2023-24-tfgii-online-feb/Proyecto_TFG_UBU_23_24/TFG/anexos.tex

\documentclass[a4paper,12pt,twoside]{memoir}

% Castellano
\usepackage[spanish,es-tabla]{babel}
\selectlanguage{spanish}
\usepackage[utf8]{inputenc}
\usepackage[T1]{fontenc}
\usepackage{lmodern} % scalable font
\usepackage{microtype}
\usepackage{placeins}
\usepackage{csquotes}
\usepackage{lscape} 
\usepackage[table,xcdraw]{xcolor}
\usepackage{graphicx}
\usepackage{float} %required for the placement specifier H

\usepackage{makecell}

\renewcommand\theadalign{bc}
\renewcommand\theadfont{\bfseries}
\renewcommand\theadgape{\Gape[4pt]}
\renewcommand\cellgape{\Gape[4pt]}

% Landscape
\usepackage{pdflscape}

% Mathematic font
\usepackage{amsfonts}

\RequirePackage{booktabs}
\RequirePackage[table]{xcolor}
\RequirePackage{xtab}
\RequirePackage{multirow}

% Multi-page tables using
\nouppercaseheads
\usepackage{longtable}
\usepackage{tabularx}

% Cell with line break (e.g. \specialcell{Foo\\bar})
\newcommand{\specialcell}[2][c]{%
  \begin{tabular}[#1]{@{}l@{}}#2\end{tabular}}
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
      \toprule
      #5
      \otoprule
    }
    \tabletail{
      \hline
      \multicolumn{#3}{r}{\small\sl continúa en la página siguiente}\\
    }
    \tablelasttail{
      \hline
    }
    \bottomcaption{#1}
    \rowcolors {2}{gray!35}{}
    \begin{xtabular}{#2}
      #6
      \bottomrule
    \end{xtabular}
    \label{tabla:#4}
  \end{center}
}

%
% Nuevo comando para tablas grandes con cabecera.
\newcommand{\tablaSinColores}[6]{%
  \begin{center}
    \tablefirsthead{
      \toprule
      #5
      \otoprule
    }
    \tablehead{
      \multicolumn{#3}{l}{\small\sl continúa desde la página anterior}\\
      \toprule
      #5
      \otoprule
    }
    \tabletail{
      \hline
      \multicolumn{#3}{r}{\small\sl continúa en la página siguiente}\\
    }
    \tablelasttail{
      \hline
    }
    \bottomcaption{#1}
    \begin{xtabular}{#2}
      #6
      \bottomrule
    \end{xtabular}
    \label{tabla:#4}
  \end{center}
}

%
% Nuevo comando para tablas grandes sin cabecera.
\newcommand{\tablaSinCabecera}[5]{%
  \begin{center}
    \tablefirsthead{
      \toprule
    }
    \tablehead{
      \multicolumn{#3}{l}{\small\sl continúa desde la página anterior}\\
      \hline
    }
    \tabletail{
      \hline
      \multicolumn{#3}{r}{\small\sl continúa en la página siguiente}\\
    }
    \tablelasttail{
      \hline
    }
    \bottomcaption{#1}
  \begin{xtabular}{#2}
    #5
   \bottomrule
  \end{xtabular}
  \label{tabla:#4}
  \end{center}
}

\definecolor{cgoLight}{HTML}{EEEEEE}
\definecolor{cgoExtralight}{HTML}{FFFFFF}

%
% Nuevo comando para tablas grandes sin cabecera.
\newcommand{\tablaSinCabeceraConBandas}[5]{%
  \begin{center}
    \tablefirsthead{
      \toprule
    }
    \tablehead{
      \multicolumn{#3}{l}{\small\sl continúa desde la página anterior}\\
      \hline
    }
    \tabletail{
      \hline
      \multicolumn{#3}{r}{\small\sl continúa en la página siguiente}\\
    }
    \tablelasttail{
      \hline
    }
    \bottomcaption{#1}
    \rowcolors[]{1}{cgoExtralight}{cgoLight}

  \begin{xtabular}{#2}
    #5
   \bottomrule
  \end{xtabular}
  \label{tabla:#4}
  \end{center}
}

\graphicspath{ {./img/} }

% Capítulos
\chapterstyle{bianchi}
\newcommand{\capitulo}[2]{
	\setcounter{chapter}{#1}
	\setcounter{section}{0}
	\setcounter{figure}{0}
	\setcounter{table}{0}
	\chapter*{#2}
	\addcontentsline{toc}{chapter}{#2}
	\markboth{#2}{#2}
}

% Apéndices
\renewcommand{\appendixname}{Apéndice}
\renewcommand*\cftappendixname{\appendixname}

\newcommand{\apendice}[1]{
	%\renewcommand{\thechapter}{A}
	\chapter{#1}
}

\renewcommand*\cftappendixname{\appendixname\ }

% Formato de portada
\makeatletter
\usepackage{xcolor}
\newcommand{\tutor}[1]{\def\@tutor{#1}}
\newcommand{\tutors}[1]{\def\@tutors{#1}}
\newcommand{\course}[1]{\def\@course{#1}}
\definecolor{cpardoBox}{HTML}{E6E6FF}
\def\maketitle{
  \null
  \thispagestyle{empty}
  % Cabecera ----------------
\noindent\vspace{1cm}%
  \vfill
  % Título proyecto y escudo informática ----------------
  \colorbox{cpardoBox}{%
    \begin{minipage}{.8\textwidth}
      \vspace{.5cm}\Large
      \begin{center}
      \textbf{TFG del Grado en Ingeniería Informática}\vspace{.6cm}\\
      \textbf{\LARGE\@title{}}
      \end{center}
      \vspace{.2cm}
    \end{minipage}

  }%
  \hfill\begin{minipage}{.20\textwidth}
    
  \end{minipage}
  \vfill
  % Datos de alumno, curso y tutores ------------------
  \begin{center}%
  {%
    \noindent\LARGE
    Presentado por \@author{}\\ 
    en Universidad de Burgos --- \@date{}\\
    Tutor: \@tutor{}\\
	Tutor: \@tutors{}\\
  }%
  \end{center}%
  \null
  \cleardoublepage
  }
\makeatother

% Datos de portada
\title{Diseño de un sistema económico IoT de monitorización de invernaderos de cannabis medicinal. \\Documentación Técnica}
\author{José Luis Caballero Martínez-Quintanilla.}
\tutor{Alejandro Merino Gómez}
\tutors{Carlos Cambra Baseca}
\date{16 de febrero de 2024}

\begin{document}

\maketitle

\cleardoublepage

%%%%%%%%%%%%%%%%%%%%%%%%%%%%%%%%%%%%%%%%%%%%%%%%%%%%%%%%%%%%%%%%%%%%%%%%%%%%%%%%%%%%%%%%

\frontmatter

\clearpage

% Indices
\tableofcontents

\clearpage

\listoffigures

\clearpage

\listoftables

\clearpage

\mainmatter

\appendix

\include{./tex/A_Plan_proyecto}
\include{./tex/B_Requisitos}
%\include{./tex/C_Diseno}
\include{./tex/D_Manual_programador}
\include{./tex/E_Manual_usuario}
%\include{./tex/F_ODS}

\bibliographystyle{plain}
\bibliography{bibliografiaAnexos}

\end{document}
