2023-24-tfgii-online-feb/Proyecto_TFG_UBU_23_24/TFG/memoria.tex

\documentclass[a4paper,12pt,twoside]{memoir}

% Castellano
\usepackage[spanish,es-tabla]{babel}
\selectlanguage{spanish}
\usepackage[utf8]{inputenc}
\usepackage[T1]{fontenc}
\usepackage{lmodern} % Scalable font
\usepackage{microtype}
\usepackage{placeins}
\usepackage{amssymb}

\RequirePackage{booktabs}
\RequirePackage[table]{xcolor}
\RequirePackage{xtab}
\RequirePackage{multirow}

% Links
\PassOptionsToPackage{hyphens}{url}\usepackage[colorlinks]{hyperref}
\hypersetup{
	allcolors = {blue}
}

% Ecuaciones
\usepackage{amsmath}

% Rutas de fichero / paquete
\newcommand{\ruta}[1]{{\sffamily #1}}

% Párrafos
\nonzeroparskip

% Huérfanas y viudas
\widowpenalty100000
\clubpenalty100000

% Imágenes
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
      \multicolumn{#3}{r}{\small\sl continúa en la página siguiente}\\
    }
    \tablelasttail{
      \hline
    }
    \bottomcaption{#1}
    \rowcolors {2}{gray!35}{}
    \begin{xtabular}{#2}
      #6
      \bottomrule
    \end{xtabular}
    \label{tabla:#4}
  \end{center}
}

%
% Nuevo comando para tablas grandes con cabecera.
\newcommand{\tablaSinColores}[6]{%
  \begin{center}
    \tablefirsthead{
      \toprule
      #5
      \otoprule
    }
    \tablehead{
      \multicolumn{#3}{l}{\small\sl continúa desde la página anterior}\\
      \toprule
      #5
      \otoprule
    }
    \tabletail{
      \hline
      \multicolumn{#3}{r}{\small\sl continúa en la página siguiente}\\
    }
    \tablelasttail{
      \hline
    }
    \bottomcaption{#1}
    \begin{xtabular}{#2}
      #6
      \bottomrule
    \end{xtabular}
    \label{tabla:#4}
  \end{center}
}

%
% Nuevo comando para tablas grandes sin cabecera.
\newcommand{\tablaSinCabecera}[5]{%
  \begin{center}
    \tablefirsthead{
      \toprule
    }
    \tablehead{
      \multicolumn{#3}{l}{\small\sl continúa desde la página anterior}\\
      \hline
    }
    \tabletail{
      \hline
      \multicolumn{#3}{r}{\small\sl continúa en la página siguiente}\\
    }
    \tablelasttail{
      \hline
    }
    \bottomcaption{#1}
  \begin{xtabular}{#2}
    #5
   \bottomrule
  \end{xtabular}
  \label{tabla:#4}
  \end{center}
}

\definecolor{cgoLight}{HTML}{EEEEEE}
\definecolor{cgoExtralight}{HTML}{FFFFFF}

%
% Nuevo comando para tablas grandes sin cabecera.
\newcommand{\tablaSinCabeceraConBandas}[5]{%
  \begin{center}
    \tablefirsthead{
      \toprule
    }
    \tablehead{
      \multicolumn{#3}{l}{\small\sl continúa desde la página anterior}\\
      \hline
    }
    \tabletail{
      \hline
      \multicolumn{#3}{r}{\small\sl continúa en la página siguiente}\\
    }
    \tablelasttail{
      \hline
    }
    \bottomcaption{#1}
    \rowcolors[]{1}{cgoExtralight}{cgoLight}

  \begin{xtabular}{#2}
    #5
   \bottomrule
  \end{xtabular}
  \label{tabla:#4}
  \end{center}
}

\graphicspath{ {./img/} }

% Capítulos
\chapterstyle{bianchi}
\newcommand{\capitulo}[2]{
	\setcounter{chapter}{#1}
	\setcounter{section}{0}
	\setcounter{figure}{0}
	\setcounter{table}{0}
	\chapter*{\thechapter.\enskip #2}
	\addcontentsline{toc}{chapter}{\thechapter.\enskip #2}
	\markboth{#2}{#2}
}

% Apéndices
\renewcommand{\appendixname}{Apéndice}
\renewcommand*\cftappendixname{\appendixname}

\newcommand{\apendice}[1]{
	%\renewcommand{\thechapter}{A}
	\chapter{#1}
}

\renewcommand*\cftappendixname{\appendixname\ }

% Formato de portada
\makeatletter
\usepackage{xcolor}
\newcommand{\tutor}[1]{\def\@tutor{#1}}
\newcommand{\tutors}[1]{\def\@tutors{#1}}
\newcommand{\course}[1]{\def\@course{#1}}
\definecolor{cpardoBox}{HTML}{E6E6FF}
\def\maketitle{
  \null
  \thispagestyle{empty}
  % Cabecera ----------------
\noindent\vspace{1cm}%
  \vfill
  % Título proyecto y escudo informática ----------------
  \colorbox{cpardoBox}{%
    \begin{minipage}{.8\textwidth}
      \vspace{.5cm}\Large
      \begin{center}
      \textbf{TFG del Grado en Ingeniería Informática}\vspace{.6cm}\\
      \textbf{\LARGE\@title{}}
      \end{center}
      \vspace{.2cm}
    \end{minipage}

  }%
  \hfill\begin{minipage}{.20\textwidth}
    
  \end{minipage}
  \vfill
  % Datos de alumno, curso y tutores ------------------
  \begin{center}%
  {%
    \noindent\LARGE
    Presentado por \@author{}\\ 
    en Universidad de Burgos --- \@date{}\\
    Tutor: \@tutor{}\\
	Tutor: \@tutors{}\\
  }%
  \end{center}%
  \null
  \cleardoublepage
  }
\makeatother

\newcommand{\nombre}{José Luis Caballero Martínez-Quintanilla.} %%% cambio de comando

% Datos de portada
\title{Diseño de un sistema económico IoT de monitorización de invernaderos de cannabis medicinal.}
\author{\nombre}
\tutor{Alejandro Merino Gómez}
\tutors{Carlos Cambra Baseca}
\date{16 de febrero de 2024}

\begin{document}

\maketitle

\newpage\null\thispagestyle{empty}\newpage

%%%%%%%%%%%%%%%%%%%%%%%%%%%%%%%%%%%%%%%%%%%%%%%%%%%%%%%%%%%%%%%%%%%%%%%%%%%%%%%%%%%%%%%%
\thispagestyle{empty}

\noindent\vspace{1cm}

\noindent D. Alejandro Merino Gómez, profesor del departamento de Digitalización, área de Systems Engineering and Automation y D. Carlos Cambra Baseca, profesor del departamento de Digitalización del área de Computer Science and Artificial Intelligence, 

\noindent Exponen:

\noindent Que el alumno D. \nombre, con DNI 48471169-A, ha realizado el Trabajo final de Grado en Ingeniería Informática titulado Diseño de un sistema económico IoT de monitorización de invernaderos de cannabis medicinal. 

\noindent Y que dicho trabajo ha sido realizado por el alumno bajo la dirección del que suscribe, en virtud de lo cual se autoriza su presentación y defensa.

\begin{center} %\large
En Burgos, {\large 16 de febrero de 2024}
\end{center}

\vfill\vfill\vfill

% Author and supervisor
\begin{minipage}{0.45\textwidth}
\begin{flushleft} %\large
Vº. Bº. del Tutor:\\[2cm]
D. Merino Gómez, Alejandro
\end{flushleft}
\end{minipage}
\hfill
\begin{minipage}{0.45\textwidth}
\begin{flushleft} %\large
Vº. Bº. del co-tutor:\\[2cm]
D. Cambra Baseca, Carlos 
\end{flushleft}
\end{minipage}
\hfill

\vfill

% para casos con solo un tutor comentar lo anterior
% y descomentar lo siguiente
%Vº. Bº. del Tutor:\\[2cm]
%D. nombre tutor

\newpage\null\thispagestyle{empty}\newpage

\frontmatter

% Abstract en castellano
\renewcommand*\abstractname{Resumen}
\begin{abstract}
El presente trabajo de fin de grado aborda el diseño de un sistema económico basado en el Internet de las cosas (IoT) para la monitorización de invernaderos destinados al cultivo de cannabis medicinal. El objetivo principal es mejorar la eficiencia y la calidad del cultivo mediante la implementación de sensores y dispositivos conectados que permitan la recolección y análisis de datos en tiempo real.

El hardware seleccionado para este proyecto incluye la Raspberry Pi Pico W como unidad central, una pantalla OLED 128x64 para la visualización de información, el sensor DHT22 para la medición de la temperatura y humedad ambiente, el sensor BH1750 para evaluar la intensidad lumínica, y un sensor de humedad de suelo para monitorear las condiciones de la tierra.

A lo largo del trabajo, se detalla el proceso de integración de estos componentes, se describen las tecnologías utilizadas para la comunicación y el manejo de datos, y se presenta la interfaz de usuario diseñada para la visualización de información relevante. Se destacan también las consideraciones económicas que han llevado a la elección de cada componente, buscando una solución asequible sin comprometer la calidad de los resultados.

Los resultados obtenidos demuestran la viabilidad y eficacia del sistema propuesto, ofreciendo a los agricultores de cannabis medicinal un instrumento práctico y accesible para mejorar la gestión de sus invernaderos. Este trabajo contribuye al campo emergente de la agricultura inteligente y sostenible, abriendo posibilidades para futuras investigaciones y aplicaciones en el ámbito de la monitorización agrícola basada en IoT.

\end{abstract}

\renewcommand*\abstractname{Descriptores}
\begin{abstract}
Raspberry Pi Pico W, Micropython, Autónomo, Sistema Domótico, Bot, Telegram, Python, MQTT, SQL \ldots
\end{abstract}

\clearpage

% Abstract en inglés
\renewcommand*\abstractname{Abstract}
\begin{abstract}
This project deals with the design of an economic system based on the Internet of Things (IoT) for the monitoring of greenhouses for the cultivation of medical cannabis. The main objective is to improve the efficiency and quality of the crop through the implementation of sensors and connected devices that allow the collection and analysis of data in real time.

The hardware selected for this project includes the Raspberry Pi Pico W as the central unit, a 128x64 OLED screen for displaying information, the DHT22 sensor for measuring ambient temperature and humidity, the BH1750 sensor for evaluating light intensity, and a soil moisture sensor for monitoring soil conditions.

Throughout the paper, the integration process of these components is detailed, the technologies used for communication and data management are described, and the user interface designed for the visualization of relevant information is presented. It also highlights the economic considerations that led to the choice of each component, seeking an affordable solution without compromising the quality of the results.

The results obtained demonstrate the feasibility and effectiveness of the proposed system, offering medical cannabis farmers a practical and accessible tool to improve the management of their greenhouses. This work contributes to the emerging field of smart and sustainable agriculture, opening possibilities for future research and applications in the field of IoT-based agricultural monitoring.
\end{abstract}

\renewcommand*\abstractname{Keywords}
\begin{abstract}
Raspberry Pi Pico W, Micropython, Autonomous, Domotic System, Bot, Telegram, Python, MQTT, SQL\ldots
\end{abstract}

\clearpage

% Indices
\tableofcontents

\clearpage

\listoffigures

\clearpage

\listoftables
\clearpage

\mainmatter
\include{./tex/1_Introduccion}
\include{./tex/2_Objetivos_del_proyecto}
\include{./tex/3_Conceptos_teoricos}
\include{./tex/4_Tecnicas_y_herramientas}
\include{./tex/5_Aspectos_relevantes_del_desarrollo_del_proyecto}
\include{./tex/6_Trabajos_relacionados}
\include{./tex/7_Conclusiones_Lineas_de_trabajo_futuras}

\bibliographystyle{plain}
\bibliography{bibliografia}

\end{document}
