2023-24-tfgii-online-feb/Proyecto_TFG_UBU_23_24/TFG/img/desarrollo/Dashboard3.png

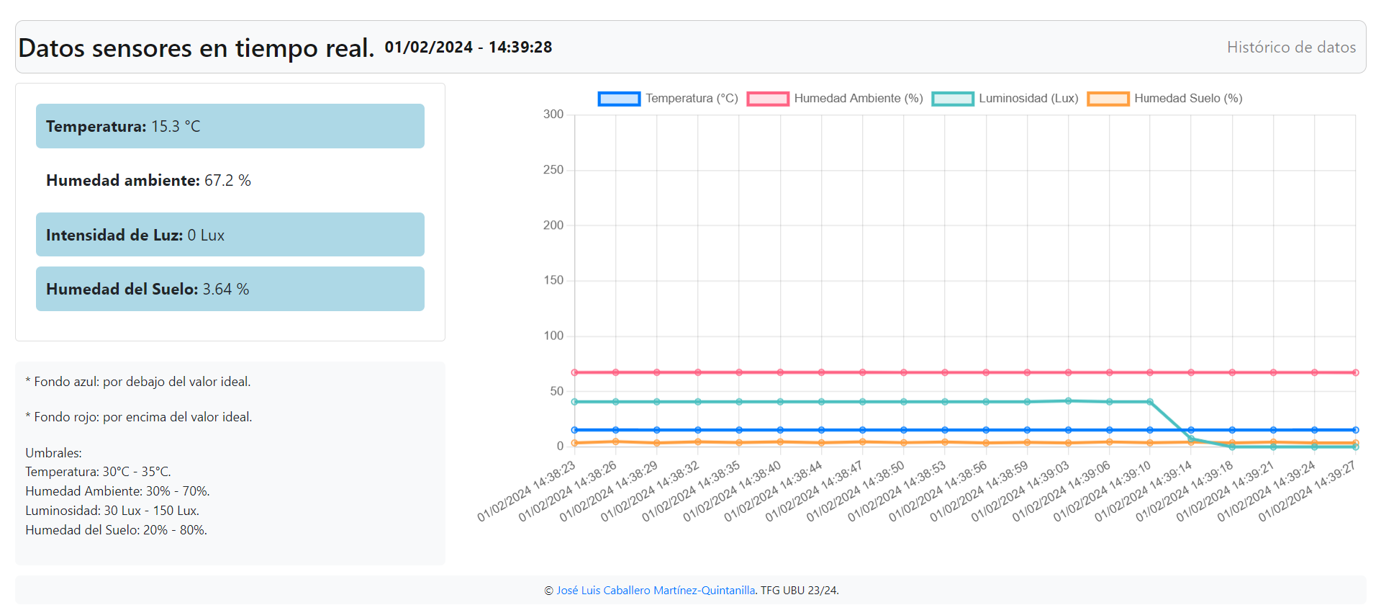
TFG/img/desarrollo/Dashboard3.png
