2023-24-tfgii-online-feb/Proyecto_TFG_UBU_23_24/TFG/img/diagramas/conexiones_protoboard.png

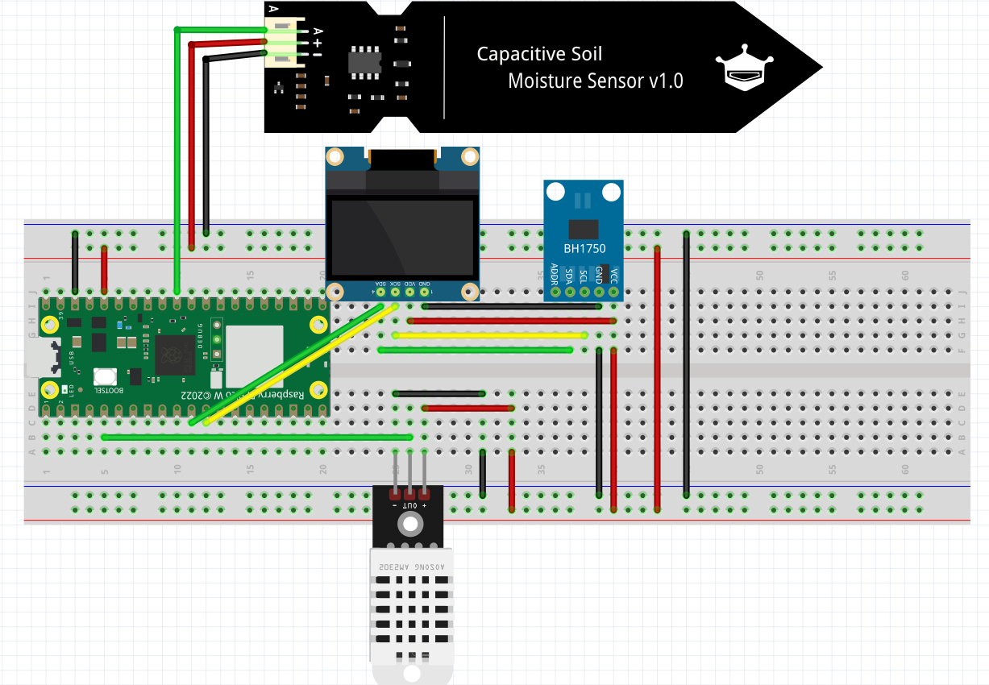
TFG/img/diagramas/conexiones_protoboard.png
