2023-24-tfgii-online-feb/Proyecto_TFG_UBU_23_24/TFG/img/diagramas/DHT22.png

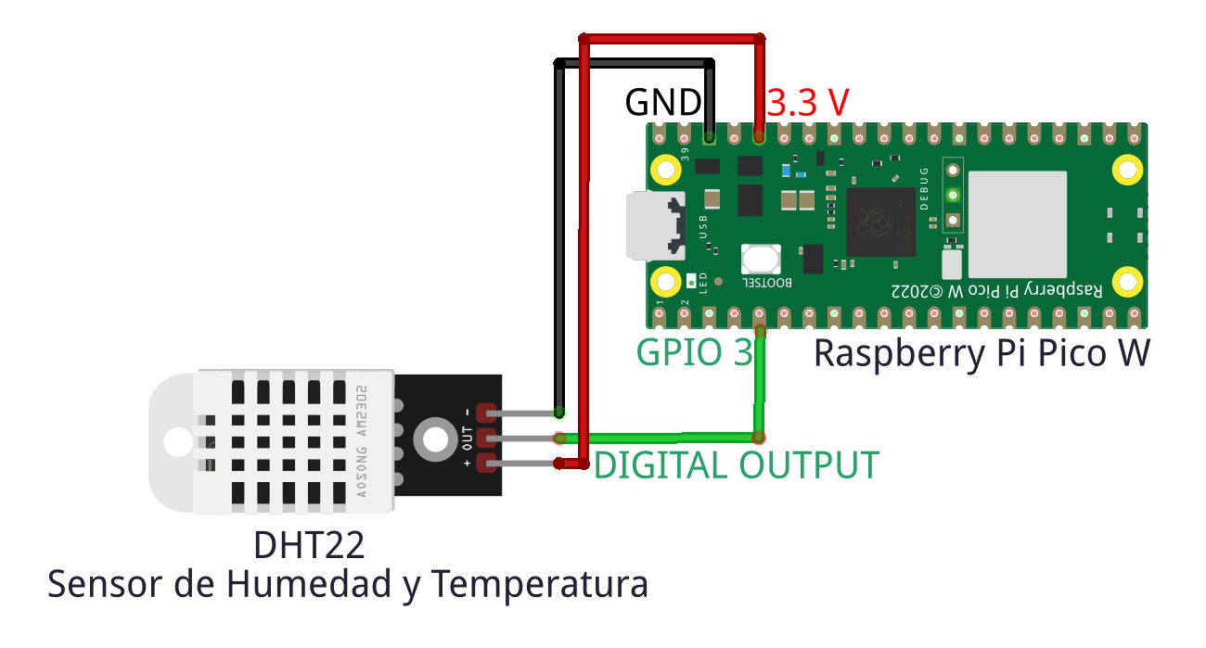
TFG/img/diagramas/DHT22.png
