2023-24-tfgii-online-feb/Proyecto_TFG_UBU_23_24/TFG/img/diagramas/directorios_nodeMqtt.png

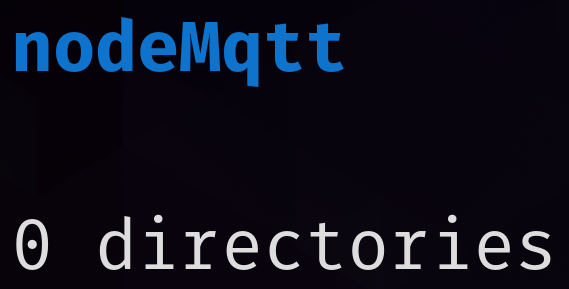
TFG/img/diagramas/directorios_nodeMqtt.png
