2023-24-tfgii-online-feb/Proyecto_TFG_UBU_23_24/TFG/img/diagramas/mqtt_InverIoT_TiempoReal.png

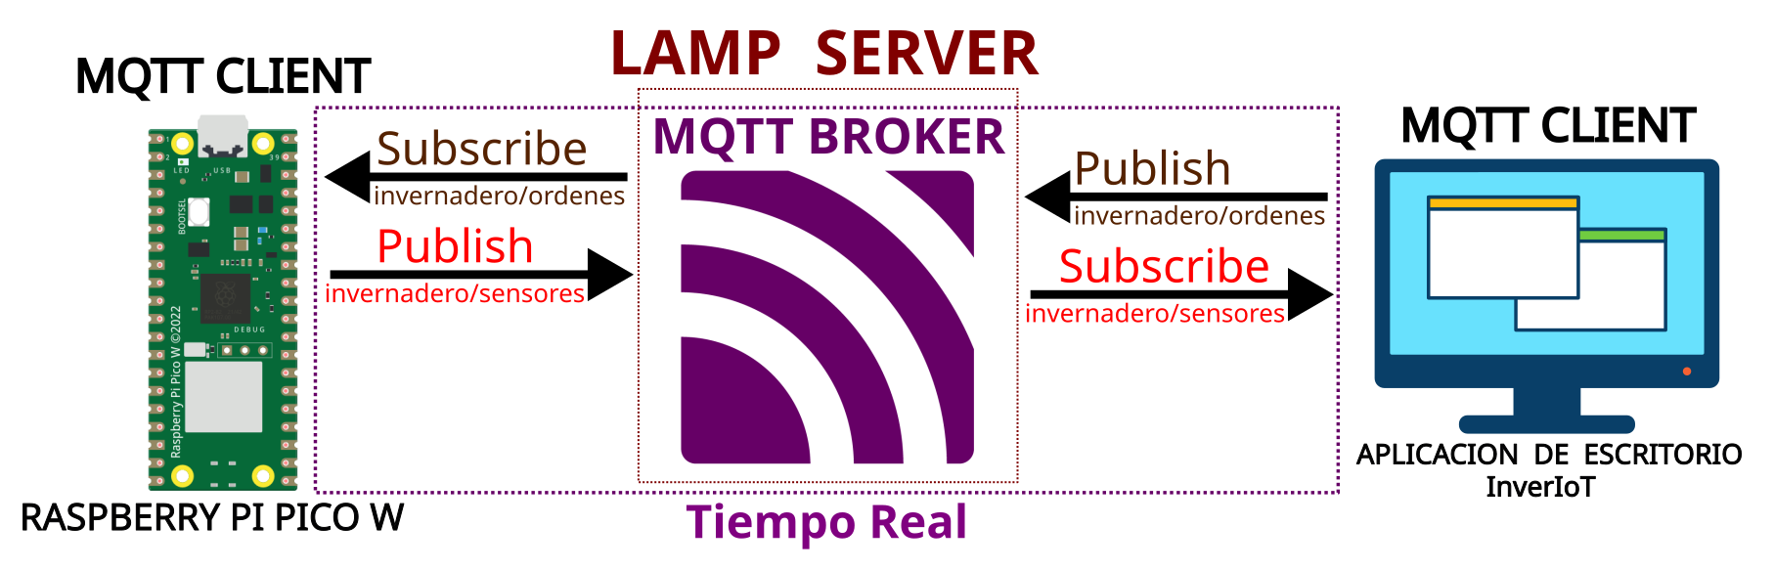
TFG/img/diagramas/mqtt_InverIoT_TiempoReal.png
