2023-24-tfgii-online-feb/Proyecto_TFG_UBU_23_24/TFG/img/fotos/foto-3.jpg

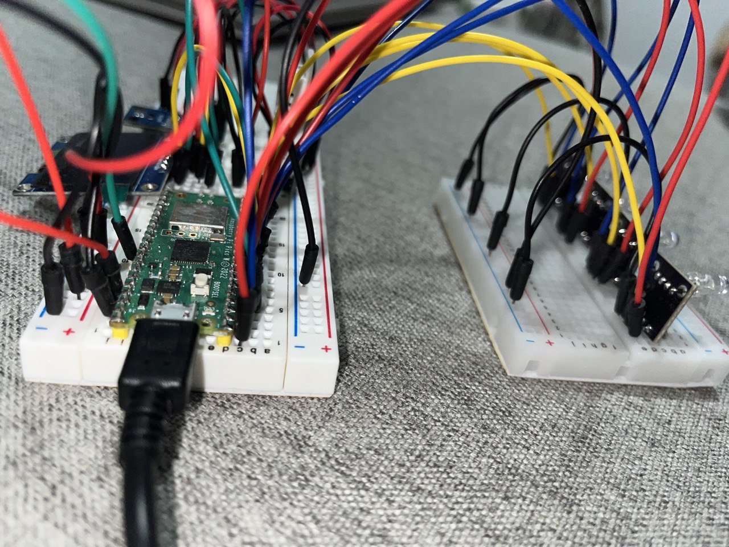
TFG/img/fotos/foto-3.jpg
