2023-24-tfgii-online-feb/Proyecto_TFG_UBU_23_24/TFG/img/fotos/panel_solar_alimentacion.png

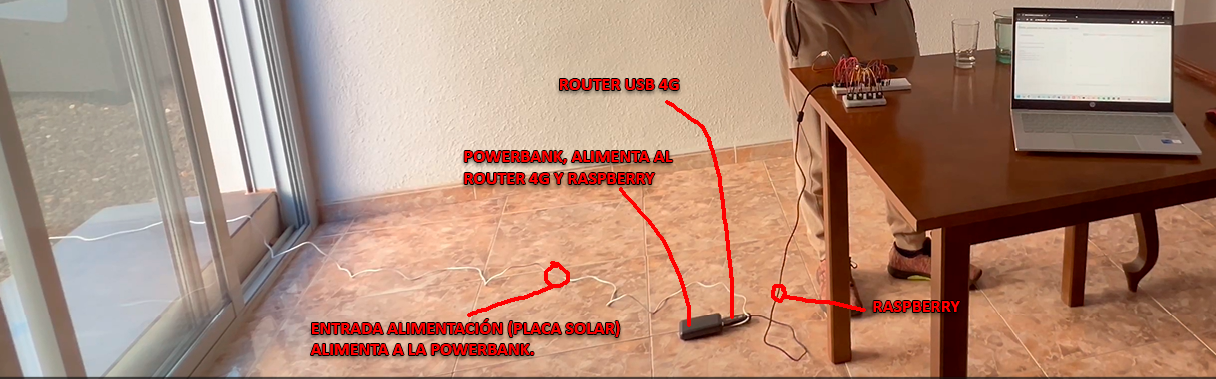
TFG/img/fotos/panel_solar_alimentacion.png
