2023-24-tfgii-online-feb/Proyecto_TFG_UBU_23_24/TFG/img/fotos/sensorHumedadSuelo.png

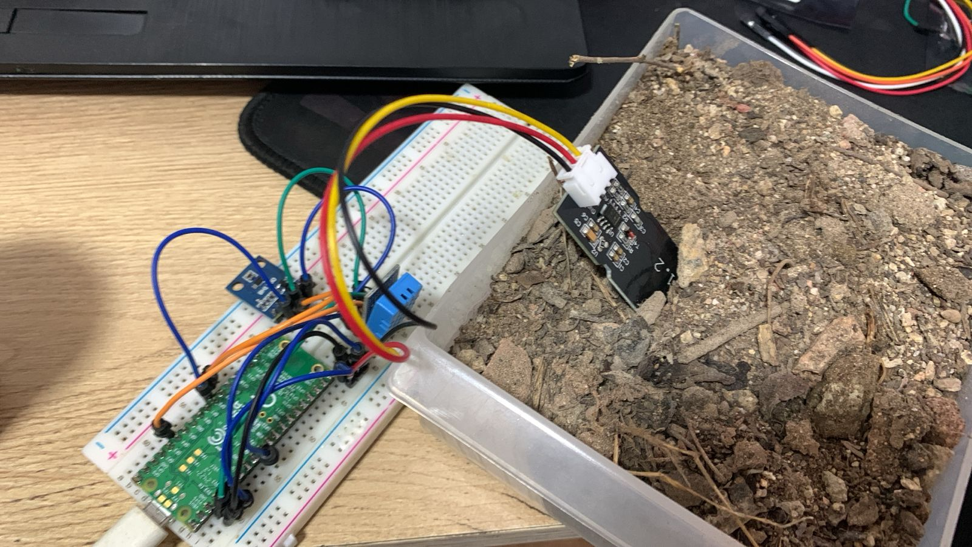
TFG/img/fotos/sensorHumedadSuelo.png
