2023-24-tfgii-online-feb/Proyecto_TFG_UBU_23_24/TFG/img/herramientas/bateria_externa_SinFondo.png

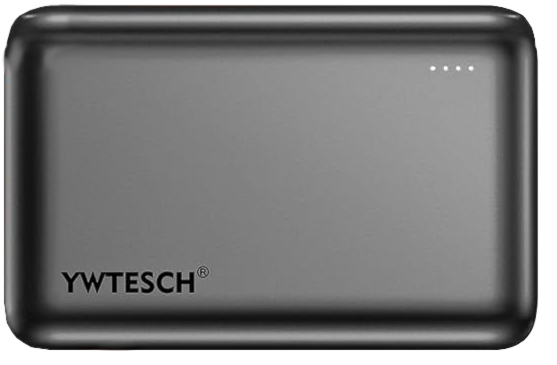
TFG/img/herramientas/bateria_externa_SinFondo.png
