2023-24-tfgii-online-feb/Proyecto_TFG_UBU_23_24/TFG/img/herramientas/bh1750_reverso.png

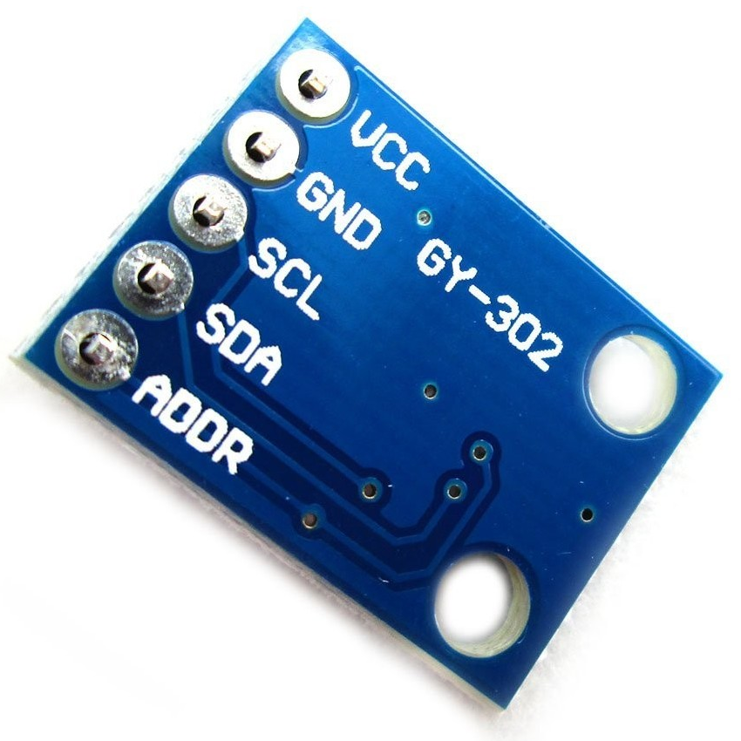
TFG/img/herramientas/bh1750_reverso.png
