2023-24-tfgii-online-feb/Proyecto_TFG_UBU_23_24/TFG/img/herramientas/dht22.png

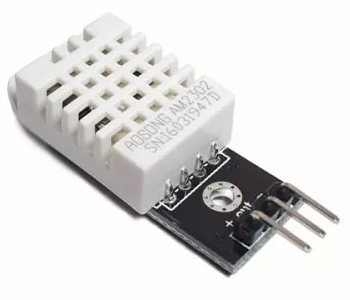
TFG/img/herramientas/dht22.png
