2023-24-tfgii-online-feb/Proyecto_TFG_UBU_23_24/TFG/img/herramientas/enrutador_wifi_SinFondo.png

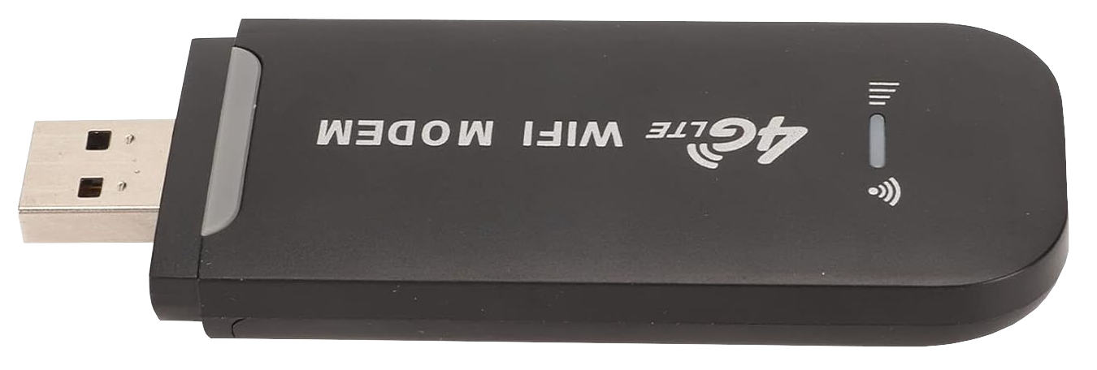
TFG/img/herramientas/enrutador_wifi_SinFondo.png
