2023-24-tfgii-online-feb/Proyecto_TFG_UBU_23_24/TFG/img/herramientas/rpipicow.png

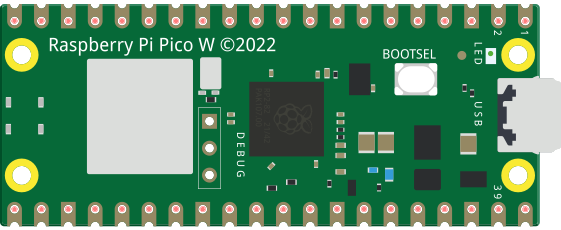
TFG/img/herramientas/rpipicow.png
