2023-24-tfgii-online-feb/Proyecto_TFG_UBU_23_24/TFG/img/herramientas/rpipicow_umqtt.png

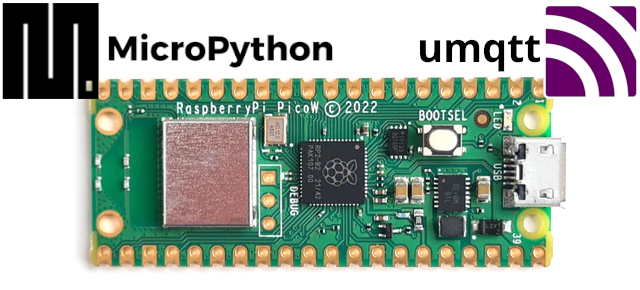
TFG/img/herramientas/rpipicow_umqtt.png
